Toroid-io/AccelerationDataLogger/Firmware/MEMS/ADXL345.h

// I2Cdev library collection - ADXL345 I2C device class header file
// Based on Analog Devices ADXL345 datasheet rev. C, 5/2011
// 7/31/2011 by Jeff Rowberg <jeff@rowberg.net>
// Updates should (hopefully) always be available at https://github.com/jrowberg/i2cdevlib
//
// Changelog:
//     2011-07-31 - initial release

/* ============================================
I2Cdev device library code is placed under the MIT license
Copyright (c) 2011 Jeff Rowberg

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
THE SOFTWARE IS PROVIDED "AS IS", WITHOUT WARRANTY OF ANY KIND, EXPRESS OR
IMPLIED, INCLUDING BUT NOT LIMITED TO THE WARRANTIES OF MERCHANTABILITY,
FITNESS FOR A PARTICULAR PURPOSE AND NONINFRINGEMENT. IN NO EVENT SHALL THE
AUTHORS OR COPYRIGHT HOLDERS BE LIABLE FOR ANY CLAIM, DAMAGES OR OTHER
LIABILITY, WHETHER IN AN ACTION OF CONTRACT, TORT OR OTHERWISE, ARISING FROM,
OUT OF OR IN CONNECTION WITH THE SOFTWARE OR THE USE OR OTHER DEALINGS IN
THE SOFTWARE.
===============================================
*/

#ifndef _ADXL345_H_
#define _ADXL345_H_

#include "I2Cdev.h"

#define ADXL345_ADDRESS_ALT_LOW     0x53 // alt address pin low (GND)
#define ADXL345_ADDRESS_ALT_HIGH    0x1D // alt address pin high (VCC)
#define ADXL345_DEFAULT_ADDRESS     ADXL345_ADDRESS_ALT_LOW

#define ADXL345_RA_DEVID            0x00
#define ADXL345_RA_RESERVED1        0x01
#define ADXL345_RA_THRESH_TAP       0x1D
#define ADXL345_RA_OFSX             0x1E
#define ADXL345_RA_OFSY             0x1F
#define ADXL345_RA_OFSZ             0x20
#define ADXL345_RA_DUR              0x21
#define ADXL345_RA_LATENT           0x22
#define ADXL345_RA_WINDOW           0x23
#define ADXL345_RA_THRESH_ACT       0x24
#define ADXL345_RA_THRESH_INACT     0x25
#define ADXL345_RA_TIME_INACT       0x26
#define ADXL345_RA_ACT_INACT_CTL    0x27
#define ADXL345_RA_THRESH_FF        0x28
#define ADXL345_RA_TIME_FF          0x29
#define ADXL345_RA_TAP_AXES         0x2A
#define ADXL345_RA_ACT_TAP_STATUS   0x2B
#define ADXL345_RA_BW_RATE          0x2C
#define ADXL345_RA_POWER_CTL        0x2D
#define ADXL345_RA_INT_ENABLE       0x2E
#define ADXL345_RA_INT_MAP          0x2F
#define ADXL345_RA_INT_SOURCE       0x30
#define ADXL345_RA_DATA_FORMAT      0x31
#define ADXL345_RA_DATAX0           0x32
#define ADXL345_RA_DATAX1           0x33
#define ADXL345_RA_DATAY0           0x34
#define ADXL345_RA_DATAY1           0x35
#define ADXL345_RA_DATAZ0           0x36
#define ADXL345_RA_DATAZ1           0x37
#define ADXL345_RA_FIFO_CTL         0x38
#define ADXL345_RA_FIFO_STATUS      0x39

#define ADXL345_AIC_ACT_AC_BIT      7
#define ADXL345_AIC_ACT_X_BIT       6
#define ADXL345_AIC_ACT_Y_BIT       5
#define ADXL345_AIC_ACT_Z_BIT       4
#define ADXL345_AIC_INACT_AC_BIT    3
#define ADXL345_AIC_INACT_X_BIT     2
#define ADXL345_AIC_INACT_Y_BIT     1
#define ADXL345_AIC_INACT_Z_BIT     0

#define ADXL345_TAPAXIS_SUP_BIT     3
#define ADXL345_TAPAXIS_X_BIT       2
#define ADXL345_TAPAXIS_Y_BIT       1
#define ADXL345_TAPAXIS_Z_BIT       0

#define ADXL345_TAPSTAT_ACTX_BIT    6
#define ADXL345_TAPSTAT_ACTY_BIT    5
#define ADXL345_TAPSTAT_ACTZ_BIT    4
#define ADXL345_TAPSTAT_ASLEEP_BIT  3
#define ADXL345_TAPSTAT_TAPX_BIT    2
#define ADXL345_TAPSTAT_TAPY_BIT    1
#define ADXL345_TAPSTAT_TAPZ_BIT    0

#define ADXL345_BW_LOWPOWER_BIT     4
#define ADXL345_BW_RATE_BIT         3
#define ADXL345_BW_RATE_LENGTH      4

#define ADXL345_RATE_3200           0b1111
#define ADXL345_RATE_1600           0b1110
#define ADXL345_RATE_800            0b1101
#define ADXL345_RATE_400            0b1100
#define ADXL345_RATE_200            0b1011
#define ADXL345_RATE_100            0b1010
#define ADXL345_RATE_50             0b1001
#define ADXL345_RATE_25             0b1000
#define ADXL345_RATE_12P5           0b0111
#define ADXL345_RATE_6P25           0b0110
#define ADXL345_RATE_3P13           0b0101
#define ADXL345_RATE_1P56           0b0100
#define ADXL345_RATE_0P78           0b0011
#define ADXL345_RATE_0P39           0b0010
#define ADXL345_RATE_0P20           0b0001
#define ADXL345_RATE_0P10           0b0000

#define ADXL345_PCTL_LINK_BIT       5
#define ADXL345_PCTL_AUTOSLEEP_BIT  4
#define ADXL345_PCTL_MEASURE_BIT    3
#define ADXL345_PCTL_SLEEP_BIT      2
#define ADXL345_PCTL_WAKEUP_BIT     1
#define ADXL345_PCTL_WAKEUP_LENGTH  2

#define ADXL345_WAKEUP_8HZ          0b00
#define ADXL345_WAKEUP_4HZ          0b01
#define ADXL345_WAKEUP_2HZ          0b10
#define ADXL345_WAKEUP_1HZ          0b11

#define ADXL345_INT_DATA_READY_BIT  7
#define ADXL345_INT_SINGLE_TAP_BIT  6
#define ADXL345_INT_DOUBLE_TAP_BIT  5
#define ADXL345_INT_ACTIVITY_BIT    4
#define ADXL345_INT_INACTIVITY_BIT  3
#define ADXL345_INT_FREE_FALL_BIT   2
#define ADXL345_INT_WATERMARK_BIT   1
#define ADXL345_INT_OVERRUN_BIT     0

#define ADXL345_FORMAT_SELFTEST_BIT 7
#define ADXL345_FORMAT_SPIMODE_BIT  6
#define ADXL345_FORMAT_INTMODE_BIT  5
#define ADXL345_FORMAT_FULL_RES_BIT 3
#define ADXL345_FORMAT_JUSTIFY_BIT  2
#define ADXL345_FORMAT_RANGE_BIT    1
#define ADXL345_FORMAT_RANGE_LENGTH 2

#define ADXL345_RANGE_2G            0b00
#define ADXL345_RANGE_4G            0b01
#define ADXL345_RANGE_8G            0b10
#define ADXL345_RANGE_16G           0b11

#define ADXL345_FIFO_MODE_BIT       7
#define ADXL345_FIFO_MODE_LENGTH    2
#define ADXL345_FIFO_TRIGGER_BIT    5
#define ADXL345_FIFO_SAMPLES_BIT    4
#define ADXL345_FIFO_SAMPLES_LENGTH 5

#define ADXL345_FIFO_MODE_BYPASS    0b00
#define ADXL345_FIFO_MODE_FIFO      0b01
#define ADXL345_FIFO_MODE_STREAM    0b10
#define ADXL345_FIFO_MODE_TRIGGER   0b11

#define ADXL345_FIFOSTAT_TRIGGER_BIT        7
#define ADXL345_FIFOSTAT_LENGTH_BIT         5
#define ADXL345_FIFOSTAT_LENGTH_LENGTH      6

void ADXL345_initialize(void);
bool ADXL345_testConnection(void);

// DEVID register
uint8_t ADXL345_getDeviceID(void);

// THRESH_TAP register
uint8_t ADXL345_getTapThreshold(void);
void ADXL345_setTapThreshold(uint8_t threshold);

// OFS* registers
void ADXL345_getOffset(int8_t* x, int8_t* y, int8_t* z);
void ADXL345_setOffset(int8_t x, int8_t y, int8_t z);
int8_t ADXL345_getOffsetX(void);
void ADXL345_setOffsetX(int8_t x);
int8_t ADXL345_getOffsetY(void);
void ADXL345_setOffsetY(int8_t y);
int8_t ADXL345_getOffsetZ(void);
void ADXL345_setOffsetZ(int8_t z);

// DUR register
uint8_t ADXL345_getTapDuration(void);
void ADXL345_setTapDuration(uint8_t duration);

// LATENT register
uint8_t ADXL345_getDoubleTapLatency(void);
void ADXL345_setDoubleTapLatency(uint8_t latency);

// WINDOW register
uint8_t ADXL345_getDoubleTapWindow(void);
void ADXL345_setDoubleTapWindow(uint8_t window);

// THRESH_ACT register
uint8_t ADXL345_getActivityThreshold(void);
void ADXL345_setActivityThreshold(uint8_t threshold);

// THRESH_INACT register
uint8_t ADXL345_getInactivityThreshold(void);
void ADXL345_setInactivityThreshold(uint8_t threshold);

// TIME_INACT register
uint8_t ADXL345_getInactivityTime(void);
void ADXL345_setInactivityTime(uint8_t time);

// ACT_INACT_CTL register
bool ADXL345_getActivityAC(void);
void ADXL345_setActivityAC(bool enabled);
bool ADXL345_getActivityXEnabled(void);
void ADXL345_setActivityXEnabled(bool enabled);
bool ADXL345_getActivityYEnabled(void);
void ADXL345_setActivityYEnabled(bool enabled);
bool ADXL345_getActivityZEnabled(void);
void ADXL345_setActivityZEnabled(bool enabled);
bool ADXL345_getInactivityAC(void);
void ADXL345_setInactivityAC(bool enabled);
bool ADXL345_getInactivityXEnabled(void);
void ADXL345_setInactivityXEnabled(bool enabled);
bool ADXL345_getInactivityYEnabled(void);
void ADXL345_setInactivityYEnabled(bool enabled);
bool ADXL345_getInactivityZEnabled(void);
void ADXL345_setInactivityZEnabled(bool enabled);

// THRESH_FF register
uint8_t ADXL345_getFreefallThreshold(void);
void ADXL345_setFreefallThreshold(uint8_t threshold);

// TIME_FF register
uint8_t ADXL345_getFreefallTime(void);
void ADXL345_setFreefallTime(uint8_t time);

// TAP_AXES register
bool ADXL345_getTapAxisSuppress(void);
void ADXL345_setTapAxisSuppress(bool enabled);
bool ADXL345_getTapAxisXEnabled(void);
void ADXL345_setTapAxisXEnabled(bool enabled);
bool ADXL345_getTapAxisYEnabled(void);
void ADXL345_setTapAxisYEnabled(bool enabled);
bool ADXL345_getTapAxisZEnabled(void);
void ADXL345_setTapAxisZEnabled(bool enabled);

// ACT_TAP_STATUS register
bool ADXL345_getActivitySourceX(void);
bool ADXL345_getActivitySourceY(void);
bool ADXL345_getActivitySourceZ(void);
bool ADXL345_getAsleep(void);
bool ADXL345_getTapSourceX(void);
bool ADXL345_getTapSourceY(void);
bool ADXL345_getTapSourceZ(void);

// BW_RATE register
bool ADXL345_getLowPowerEnabled(void);
void ADXL345_setLowPowerEnabled(bool enabled);
uint8_t ADXL345_getRate(void);
void ADXL345_setRate(uint8_t rate);

// POWER_CTL register
bool ADXL345_getLinkEnabled(void);
void ADXL345_setLinkEnabled(bool enabled);
bool ADXL345_getAutoSleepEnabled(void);
void ADXL345_setAutoSleepEnabled(bool enabled);
bool ADXL345_getMeasureEnabled(void);
void ADXL345_setMeasureEnabled(bool enabled);
bool ADXL345_getSleepEnabled(void);
void ADXL345_setSleepEnabled(bool enabled);
uint8_t ADXL345_getWakeupFrequency(void);
void ADXL345_setWakeupFrequency(uint8_t frequency);

// INT_ENABLE register
bool ADXL345_getIntDataReadyEnabled(void);
void ADXL345_setIntDataReadyEnabled(bool enabled);
bool ADXL345_getIntSingleTapEnabled(void);
void ADXL345_setIntSingleTapEnabled(bool enabled);
bool ADXL345_getIntDoubleTapEnabled(void);
void ADXL345_setIntDoubleTapEnabled(bool enabled);
bool ADXL345_getIntActivityEnabled(void);
void ADXL345_setIntActivityEnabled(bool enabled);
bool ADXL345_getIntInactivityEnabled(void);
void ADXL345_setIntInactivityEnabled(bool enabled);
bool ADXL345_getIntFreefallEnabled(void);
void ADXL345_setIntFreefallEnabled(bool enabled);
bool ADXL345_getIntWatermarkEnabled(void);
void ADXL345_setIntWatermarkEnabled(bool enabled);
bool ADXL345_getIntOverrunEnabled(void);
void ADXL345_setIntOverrunEnabled(bool enabled);

// INT_MAP register
uint8_t ADXL345_getIntDataReadyPin(void);
void ADXL345_setIntDataReadyPin(uint8_t pin);
uint8_t ADXL345_getIntSingleTapPin(void);
void ADXL345_setIntSingleTapPin(uint8_t pin);
uint8_t ADXL345_getIntDoubleTapPin(void);
void ADXL345_setIntDoubleTapPin(uint8_t pin);
uint8_t ADXL345_getIntActivityPin(void);
void ADXL345_setIntActivityPin(uint8_t pin);
uint8_t ADXL345_getIntInactivityPin(void);
void ADXL345_setIntInactivityPin(uint8_t pin);
uint8_t ADXL345_getIntFreefallPin(void);
void ADXL345_setIntFreefallPin(uint8_t pin);
uint8_t ADXL345_getIntWatermarkPin(void);
void ADXL345_setIntWatermarkPin(uint8_t pin);
uint8_t ADXL345_getIntOverrunPin(void);
void ADXL345_setIntOverrunPin(uint8_t pin);

// INT_SOURCE register
uint8_t ADXL345_getIntDataReadySource(void);
uint8_t ADXL345_getIntSingleTapSource(void);
uint8_t ADXL345_getIntDoubleTapSource(void);
uint8_t ADXL345_getIntActivitySource(void);
uint8_t ADXL345_getIntInactivitySource(void);
uint8_t ADXL345_getIntFreefallSource(void);
uint8_t ADXL345_getIntWatermarkSource(void);
uint8_t ADXL345_getIntOverrunSource(void);

// DATA_FORMAT register
uint8_t ADXL345_getSelfTestEnabled(void);
void ADXL345_setSelfTestEnabled(uint8_t enabled);
uint8_t ADXL345_getSPIMode(void);
void ADXL345_setSPIMode(uint8_t mode);
uint8_t ADXL345_getInterruptMode(void);
void ADXL345_setInterruptMode(uint8_t mode);
uint8_t ADXL345_getFullResolution(void);
void ADXL345_setFullResolution(uint8_t resolution);
uint8_t ADXL345_getDataJustification(void);
void ADXL345_setDataJustification(uint8_t justification);
uint8_t ADXL345_getRange(void);
void ADXL345_setRange(uint8_t range);

// DATA* registers
void ADXL345_getAcceleration(int16_t* x, int16_t* y, int16_t* z);
int16_t ADXL345_getAccelerationX(void);
int16_t ADXL345_getAccelerationY(void);
int16_t ADXL345_getAccelerationZ(void);

// FIFO_CTL register
uint8_t ADXL345_getFIFOMode(void);
void ADXL345_setFIFOMode(uint8_t mode);
uint8_t ADXL345_getFIFOTriggerInterruptPin(void);
void ADXL345_setFIFOTriggerInterruptPin(uint8_t interrupt);
uint8_t ADXL345_getFIFOSamples(void);
void ADXL345_setFIFOSamples(uint8_t size);

// FIFO_STATUS register
bool ADXL345_getFIFOTriggerOccurred(void);
uint8_t ADXL345_getFIFOLength(void);


#endif /* _ADXL345_H_ */
