Toroid-io/AccelerationDataLogger/Qt/aboutme.cpp

#include "aboutme.h"
#include "ui_aboutme.h"

AboutMe::AboutMe(QWidget *parent) :
    QDialog(parent),
    ui(new Ui::AboutMe)
{
    ui->setupUi(this);
    connect(ui->closeButton,
            &QPushButton::clicked, this,
            &AboutMe::close);
}

AboutMe::~AboutMe()
{
    delete ui;
}
